Aodrulez/zenFlow/pcb/output/pcbs/zenFlow.png

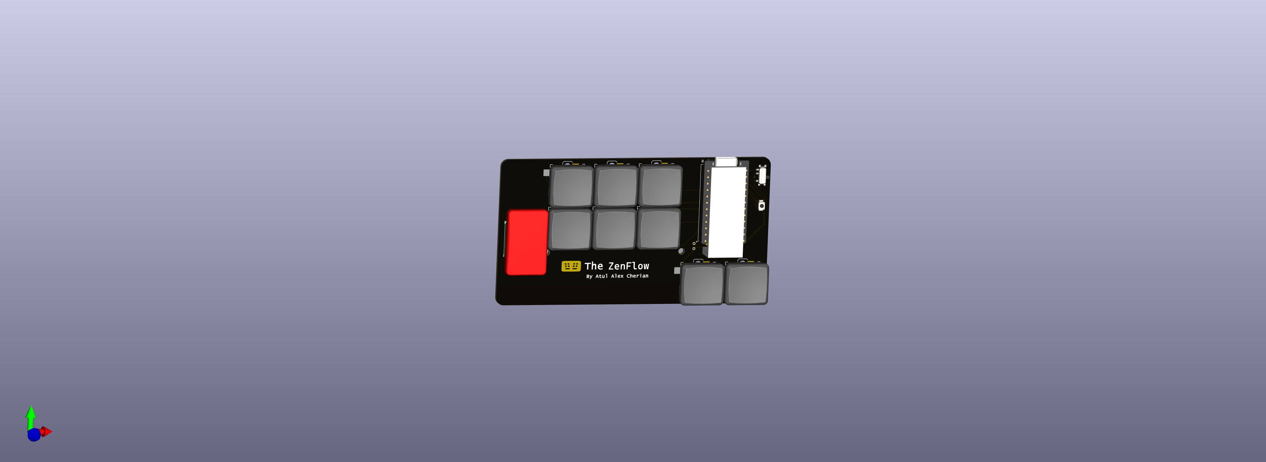
pcb/output/pcbs/zenFlow.png
